trachvik/3D_Printer_Controller/code/3D_Printer_Controller/src/source_files/MCP23017.cpp

#include "header_files/MCP23017.h"

MCP23017::MCP23017()
    : Adafruit_MCP23X17()
{
}

bool MCP23017::init()
{
    if (!begin_I2C()) {
        Serial.println("Error inicializing MCP23017!");
        return false;
    }
    return true;
}
